xyphro/HP3457-OLED-display/software/source/HP3457Oled/icons.c

#include "icons.h"

const uint8_t icon_2ohm[] PROGMEM = 
{
	0x00, 0xfe, 0xfe, 0xfe, 0xfe, 0xfe, 0xfe, 0xfe, 0xfe, 0xfe, 0x00,  // column # 0
	0x00, 0xff, 0x87, 0xf7, 0xef, 0xdf, 0xbf, 0xb7, 0xcf, 0xff, 0x00,  // column # 1
	0x00, 0xff, 0xcc, 0xed, 0xed, 0xde, 0xde, 0xed, 0xf3, 0xff, 0x00,  // column # 2
	0x00, 0x7f, 0x7f, 0x7f, 0x7f, 0x7f, 0x7f, 0x7f, 0x7f, 0x7f, 0x00,  // column # 3
};

const uint8_t icon_2ohm_big[] PROGMEM = 
{
	0x00, 0x00, 0x00, 0x00, 0x00, 0x00, 0x00, 0x00, 0x00, 0x00, 0x00,  // column # 0
	0x00, 0x3e, 0x06, 0x0c, 0x1c, 0x38, 0x30, 0x30, 0x36, 0x1c, 0x00,  // column # 1
	0x00, 0x33, 0x12, 0x12, 0x33, 0x33, 0x33, 0x33, 0x33, 0x1e, 0x00,  // column # 2
	0x00, 0x00, 0x00, 0x00, 0x00, 0x00, 0x00, 0x00, 0x00, 0x00, 0x00,  // column # 3
};

const uint8_t icon_4ohm[] PROGMEM = 
{
	0x00, 0xfe, 0xfe, 0xfe, 0xfe, 0xfe, 0xfe, 0xfe, 0xfe, 0xfe, 0x00,  // column # 0
	0x00, 0xff, 0xdf, 0xdf, 0x83, 0xdb, 0xd7, 0xcf, 0xdf, 0xff, 0x00,  // column # 1
	0x00, 0xff, 0xcc, 0xed, 0xed, 0xde, 0xde, 0xed, 0xf3, 0xff, 0x00,  // column # 2
	0x00, 0x7f, 0x7f, 0x7f, 0x7f, 0x7f, 0x7f, 0x7f, 0x7f, 0x7f, 0x00,  // column # 3
};

const uint8_t icon_4ohm_big[] PROGMEM = 
{
	0x00, 0x00, 0x00, 0x00, 0x00, 0x00, 0x00, 0x00, 0x00, 0x00, 0x00,  // column # 0
	0x00, 0x18, 0x18, 0x3e, 0x1a, 0x1a, 0x1c, 0x1c, 0x18, 0x18, 0x00,  // column # 1
	0x00, 0x33, 0x12, 0x12, 0x33, 0x33, 0x33, 0x33, 0x33, 0x1e, 0x00,  // column # 2
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
	0x80, 0xc0, 0xe0, 0xf0, 0xf8, 0xfc, 0xfe, 0xff, 0xff, 0xff, 0xff,  // column # 1
	0x00, 0x01, 0x03, 0x07, 0x0f, 0x1f, 0x3f, 0x7f, 0xff, 0xff, 0xff,  // column # 2
	0x00, 0x00, 0x00, 0x00, 0x00, 0x00, 0x00, 0x00, 0x00, 0x01, 0x03,  // column # 3
};
