xyphro/HP3457-OLED-display/software/source/HP3457Oled/gfxelements.h

#ifndef __GFXELEMENTS_H
#define __GFXELEMENTS_H
#include <avr/pgmspace.h>

#include <stdint.h>
#include <stdbool.h>

extern const uint8_t segmentmap[] PROGMEM;
extern const uint16_t kommalimits[];

#endif
