xyphro/HP3457-OLED-display/software/source/HP3457Oled/icons.h

#ifndef __ICONS_H
#define __ICONS_H

#include <stdint.h>
#include <avr/pgmspace.h>

extern const uint8_t icon_2ohm[] PROGMEM;
extern const uint8_t icon_2ohm_big[] PROGMEM;
extern const uint8_t icon_4ohm[] PROGMEM;
extern const uint8_t icon_4ohm_big[] PROGMEM;
extern const uint8_t icon_4wo[] PROGMEM;
extern const uint8_t icon_4wo_big[] PROGMEM;
extern const uint8_t icon_acpdc[] PROGMEM;
extern const uint8_t icon_acpdc_big[] PROGMEM;
extern const uint8_t icon_adrs[] PROGMEM;
extern const uint8_t icon_adrs_big[] PROGMEM;
extern const uint8_t icon_azoff[] PROGMEM;
extern const uint8_t icon_azoff_big[] PROGMEM;
extern const uint8_t icon_cal[] PROGMEM;
extern const uint8_t icon_cal_big[] PROGMEM;
extern const uint8_t icon_err[] PROGMEM;
extern const uint8_t icon_err_big[] PROGMEM;
extern const uint8_t icon_lstn[] PROGMEM;
extern const uint8_t icon_lstn_big[] PROGMEM;
extern const uint8_t icon_math[] PROGMEM;
extern const uint8_t icon_math_big[] PROGMEM;
extern const uint8_t icon_mrng[] PROGMEM;
extern const uint8_t icon_mrng_big[] PROGMEM;
extern const uint8_t icon_rear[] PROGMEM;
extern const uint8_t icon_rear_big[] PROGMEM;
extern const uint8_t icon_rem[] PROGMEM;
extern const uint8_t icon_rem_big[] PROGMEM;
extern const uint8_t icon_rmt[] PROGMEM;
extern const uint8_t icon_rmt_big[] PROGMEM;
extern const uint8_t icon_sample[] PROGMEM;
extern const uint8_t icon_sample_big[] PROGMEM;
extern const uint8_t icon_shift[] PROGMEM;
extern const uint8_t icon_shift_big[] PROGMEM;
extern const uint8_t icon_srq[] PROGMEM;
extern const uint8_t icon_srq_big[] PROGMEM;
extern const uint8_t icon_strg[] PROGMEM;
extern const uint8_t icon_strg_big[] PROGMEM;
extern const uint8_t icon_tlk[] PROGMEM;
extern const uint8_t icon_tlk_big[] PROGMEM;
extern const uint8_t icon_triangle[] PROGMEM;

#endif
